schl3sch/audiTim/Blender/PNGs/RoomPicAngle.png

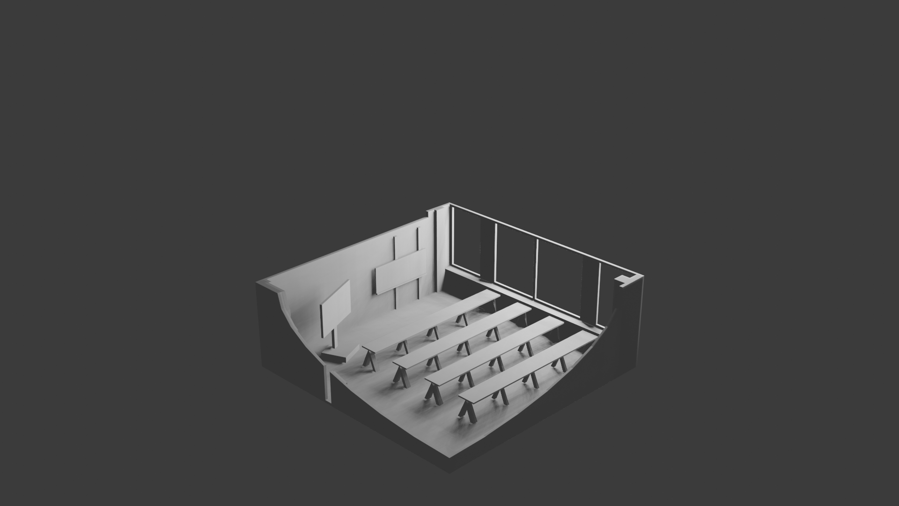
Blender/PNGs/RoomPicAngle.png
