schl3sch/audiTim/Blender/PNGs/RoomPicTopDown.png

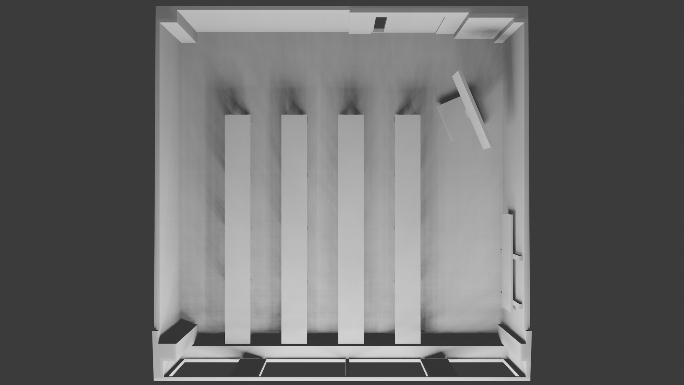
Blender/PNGs/RoomPicTopDown.png
