schl3sch/audiTim/Documentation/ProjektSe/images/3DPrinting/SensorStandALT.png

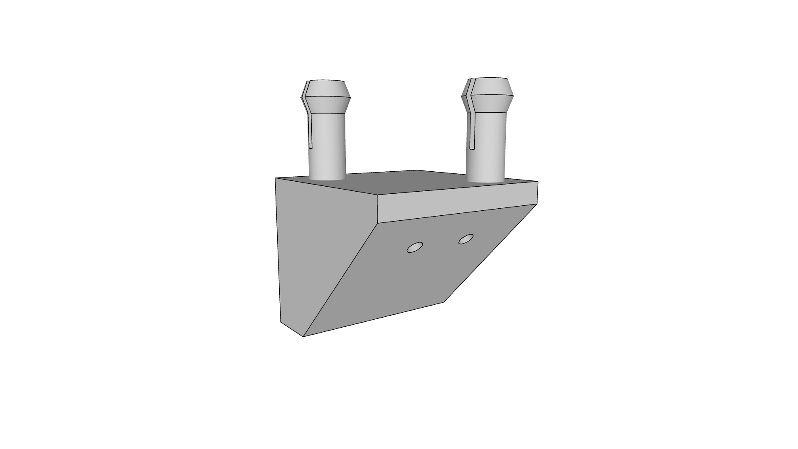
Documentation/ProjektSe/images/3DPrinting/SensorStandALT.png
