schl3sch/audiTim/Blender/PinstraightWslitx1_05.stl

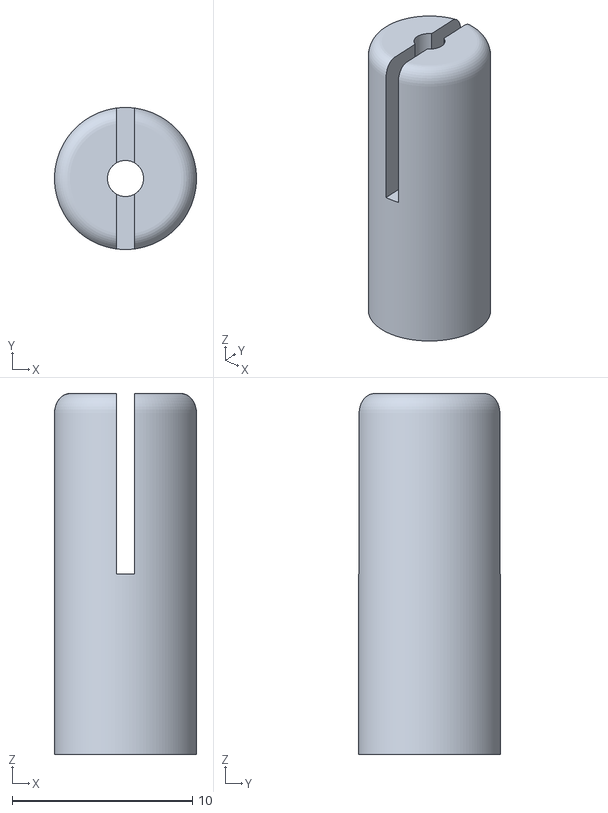
[picture p54: CAD file, 2025-08-08]
Blender/PinstraightWslitx1_05.stl
7.88 x 7.87 x 20.0
