schl3sch/audiTim/Blender/Pinstraightx1_1.stl

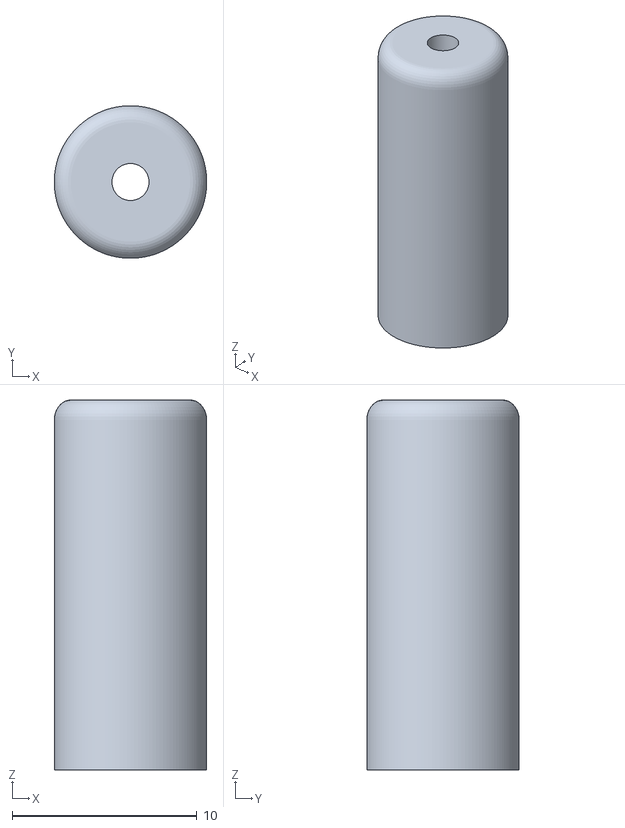
[picture p55: CAD file, 2025-08-08]
Blender/Pinstraightx1_1.stl
8.25 x 8.25 x 20.0
