schl3sch/audiTim/Blender/SensorHolder.stl

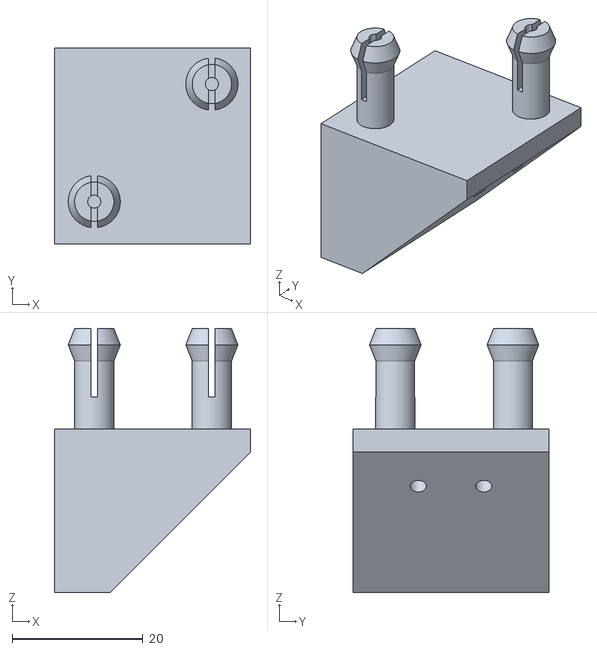
[picture p56: CAD file, 2025-07-31]
Blender/SensorHolder.stl
30.0 x 30.0 x 40.4
